jeremyrapalo6-collab/Starfall/production/Purple_Inlays_Print_Layout.STEP

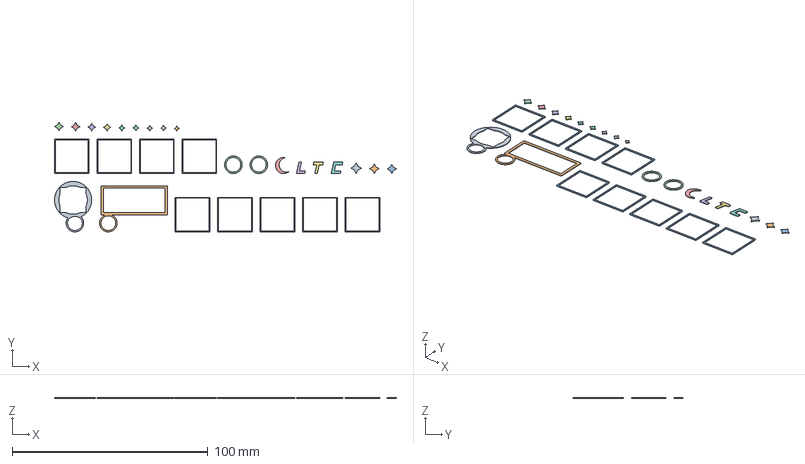
[picture p26: CAD file, 2026-09-18]
production/Purple_Inlays_Print_Layout.STEP
174.7 x 56.1 x 0.483 mm
