jeremyrapalo6-collab/Starfall/CAD/Starfall_fit_reference_1p6mm.STEP

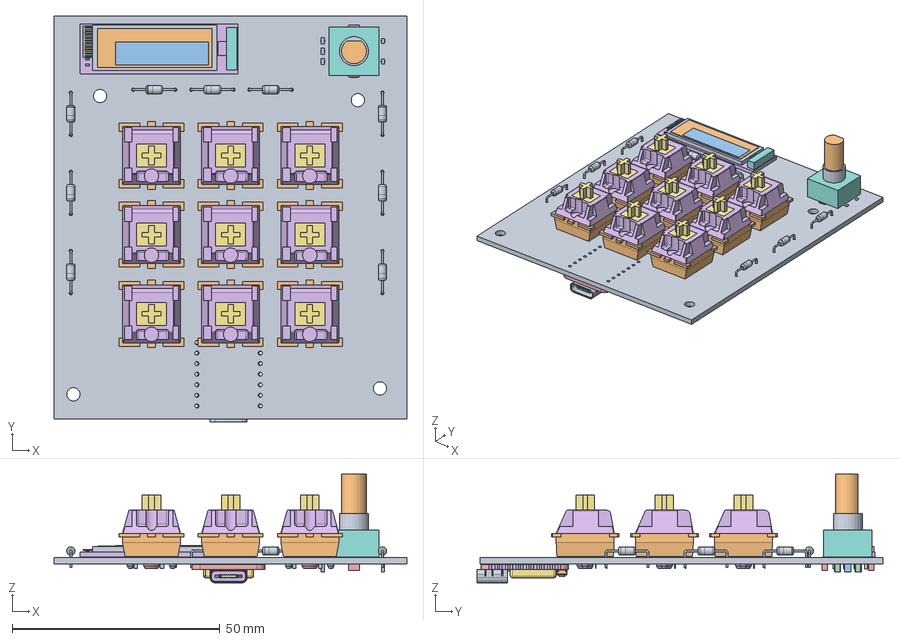
[picture p27: CAD file, 2026-09-18]
CAD/Starfall_fit_reference_1p6mm.STEP
84.9 x 97.7 x 26.2 mm
